mateusznowakdev/door-controller/firmware/app/core.py

import asyncio
import board
import keypad
import rtc as _rtc
import time
from busio import I2C
from digitalio import DigitalInOut, Direction, Pull
from microcontroller import watchdog
from pwmio import PWMOut
from watchdog import WatchDogMode

from adafruit_24lc32 import EEPROM_I2C
from adafruit_character_lcd.character_lcd import Character_LCD_Mono
from adafruit_ds3231 import DS3231

from app import const
from app.shared import _, get_checksum, get_time_offsets, log, verify_checksum
from app.types import HistoryT, SettingsT, TaskT

WDT_PIN = board.GP28

LCD_RS_PIN = board.GP9
LCD_EN_PIN = board.GP8
LCD_DB4_PIN = board.GP7
LCD_DB5_PIN = board.GP6
LCD_DB6_PIN = board.GP5
LCD_DB7_PIN = board.GP4
LCD_BL_PIN = board.GP3

KEY_LEFT_PIN = board.GP13
KEY_RIGHT_PIN = board.GP14
KEY_ENTER_PIN = board.GP15

I2C_SCL_PIN = board.GP11
I2C_SDA_PIN = board.GP10


class _WatchDog:
    TIMEOUT = 8.0

    def __init__(self) -> None:
        self.wdt_pin = DigitalInOut(WDT_PIN)
        self.wdt_pin.direction = Direction.INPUT
        self.wdt_pin.pull = Pull.DOWN
        self.enabled = False

    def feed(self) -> None:
        # watchdog will be enabled as soon as wdt_pin is detected to be HIGH,
        # and it cannot be disabled until restart

        if not self.enabled and self.wdt_pin.value is True:
            watchdog.timeout = self.TIMEOUT
            watchdog.mode = WatchDogMode.RESET
            self.enabled = True

            log("Watchdog initialized")

        if self.enabled:
            watchdog.feed()


class _Logger:
    FIRST_BYTE = 1024
    LAST_BYTE = 2048

    FRAME_SIZE = 8

    END_FRAME = [255, 0, 0, 0, 0, 0, 0]
    END_FRAME.append(get_checksum(END_FRAME))

    def __init__(self) -> None:
        self.address = self.FIRST_BYTE

        # copy EEPROM to RAM
        raw = eeprom[self.FIRST_BYTE : self.LAST_BYTE]

        for address in range(self.FIRST_BYTE, self.LAST_BYTE, self.FRAME_SIZE):
            first = address - self.FIRST_BYTE
            last = first + self.FRAME_SIZE

            if raw[first:last] == bytearray(self.END_FRAME):
                # found location for the next write
                self.address = address
                break

    def get(self, log_id: int) -> HistoryT:
        # self.address is the location of the end frame
        # so the #0 is self.address-8
        #        #1 is self.address-16, and so on
        address = self.address - (log_id + 1) * self.FRAME_SIZE

        # handle wraparound
        while address < self.FIRST_BYTE:
            address += self.LAST_BYTE - self.FIRST_BYTE

        raw = eeprom[address : address + self.FRAME_SIZE]
        if not verify_checksum(raw):
            return HistoryT(255, 0, 0, 0)

        return HistoryT(raw[0], raw[1], raw[2], raw[3])

    def log(self, message_id: int) -> None:
        log(_(message_id))

        now = time.localtime()

        raw = [message_id, now.tm_hour, now.tm_min, now.tm_sec, 0, 0, 0]
        raw.append(get_checksum(raw))

        # write log data
        first = self.address
        last = first + self.FRAME_SIZE
        eeprom[first:last] = bytearray(raw)
        self.address += self.FRAME_SIZE

        # handle wraparound
        if self.address >= self.LAST_BYTE:
            self.address = self.FIRST_BYTE

        # write end frame data
        # the same address will be used for next log write
        first = self.address
        last = first + self.FRAME_SIZE
        eeprom[first:last] = self.END_FRAME


class _Motor:
    # action ID describes the first EEPROM address for its settings
    ACT_OPEN = 512
    ACT_CLOSE = 512 + 8

    REASON_ONESHOT = 0
    REASON_AUTO = 1
    REASON_MEASURE = 2

    def __init__(self) -> None:
        self.lock = None

        self._ch1 = DigitalInOut(board.GP18)
        self._ch1.direction = Direction.OUTPUT
        self._ch1.value = False

        self._ch2 = DigitalInOut(board.GP19)
        self._ch2.direction = Direction.OUTPUT
        self._ch2.value = False

        self._ch3 = DigitalInOut(board.GP20)
        self._ch3.direction = Direction.OUTPUT
        self._ch3.value = False

        self._ch4 = DigitalInOut(board.GP21)
        self._ch4.direction = Direction.OUTPUT
        self._ch4.value = False

    def sleep(self, duration: float) -> None:
        loop_duration = wdt.TIMEOUT / 2

        while duration > 0:
            wdt.feed()
            time.sleep(loop_duration if duration > loop_duration else duration)
            duration -= loop_duration

        wdt.feed()

    async def asleep(self, duration: float) -> None:
        loop_duration = 0.5

        while duration > 0:
            wdt.feed()
            await asyncio.sleep(loop_duration if duration > loop_duration else duration)
            duration -= loop_duration

        wdt.feed()

    def open_start(self, reason_id: int) -> bool:
        if self.lock:
            return False

        logger.log(const.ACT_OPEN_START + reason_id)

        self.lock = object()
        self._ch1.value = False
        self._ch2.value = True

        return True

    def open_stop(self) -> None:
        self._ch1.value = False
        self._ch2.value = False
        self.lock = None

        logger.log(const.ACT_OPEN_STOP)

    def open(self, reason_id: int, duration: float) -> None:
        if not self.open_start(reason_id):
            return

        self.sleep(duration)
        self.open_stop()

    async def aopen(self, reason_id: int, duration: float) -> None:
        if not self.open_start(reason_id):
            return

        try:
            await self.asleep(duration)
        finally:
            self.open_stop()

    def close_start(self, reason_id: int) -> bool:
        if self.lock:
            return False

        logger.log(const.ACT_CLOSE_START + reason_id)

        self.lock = object()
        self._ch3.value = False
        self._ch4.value = True

        return True

    def close_stop(self) -> None:
        self._ch3.value = False
        self._ch4.value = False
        self.lock = None

        logger.log(const.ACT_CLOSE_STOP)

    def close(self, reason_id: int, duration: float) -> None:
        if not self.close_start(reason_id):
            return

        self.sleep(duration)
        self.close_stop()

    async def aclose(self, reason_id: int, duration: float) -> None:
        if not self.close_start(reason_id):
            return

        try:
            await self.asleep(duration)
        finally:
            self.close_stop()


class _Display:
    WIDTH = 16
    HEIGHT = 2

    BACKLIGHT_HIGH = 50
    BACKLIGHT_LOW = 15
    BACKLIGHT_OFF = 1

    CHAR_OPEN = 0, 0b11000, 0b10110, 0b10001, 0b10110, 0b11000, 0, 0
    CHAR_CLOSE = 0, 0b00011, 0b01101, 0b10001, 0b01101, 0b00011, 0, 0
    CHAR_SET_OPEN = 0, 0b11000, 0b10110, 0b00001, 0b11010, 0b11000, 0, 0
    CHAR_SET_CLOSE = 0, 0b00011, 0b01101, 0b10000, 0b01011, 0b00011, 0, 0
    CHAR_SET_SYSTEM = 0, 0b00100, 0b00010, 0b10010, 0b01110, 0b00001, 0, 0
    CHAR_TIME = 0, 0b01110, 0b10101, 0b10111, 0b10001, 0b01110, 0, 0
    CHAR_OK = 0, 0b00001, 0b00010, 0b00100, 0b10100, 0b01000, 0, 0
    CHAR_CANCEL = 0, 0b10001, 0b01010, 0b00100, 0b01010, 0b10001, 0, 0
    CHAR_CURSOR_L = 0b00101, 0b00000, 0b00100, 0, 0, 0b00100, 0b00000, 0b00101
    CHAR_CURSOR_R = 0b10100, 0b00000, 0b00100, 0, 0, 0b00100, 0b00000, 0b10100
    CHAR_CURSOR_ALT_L = 0b00111, 0b00100, 0b00100, 0, 0, 0b00100, 0b00100, 0b00111
    CHAR_CURSOR_ALT_R = 0b11100, 0b00100, 0b00100, 0, 0, 0b00100, 0b00100, 0b11100

    def __init__(self) -> None:
        self._display = Character_LCD_Mono(
            rs=DigitalInOut(LCD_RS_PIN),
            en=DigitalInOut(LCD_EN_PIN),
            db4=DigitalInOut(LCD_DB4_PIN),
            db5=DigitalInOut(LCD_DB5_PIN),
            db6=DigitalInOut(LCD_DB6_PIN),
            db7=DigitalInOut(LCD_DB7_PIN),
            columns=self.WIDTH,
            lines=self.HEIGHT,
        )
        self._display.create_char(0, self.CHAR_OPEN)
        self._display.create_char(1, self.CHAR_CLOSE)
        self.set_default_icons()
        self._display.create_char(4, self.CHAR_SET_SYSTEM)
        self._display.create_char(5, self.CHAR_TIME)
        self.set_default_cursor()

        self._cur_buffer = bytearray(b" " * self.WIDTH * self.HEIGHT)
        self._old_buffer = self._cur_buffer[:]
        self.clear()

        self._backlight = PWMOut(LCD_BL_PIN)
        self.set_backlight(self.BACKLIGHT_OFF)

    def clear(self) -> None:
        self._cur_buffer[:] = b" " * len(self._cur_buffer)

    def write(self, pos: tuple[int, int], data: bytes) -> None:
        col, row = pos
        byte_id = row * self.WIDTH + col

        self._cur_buffer[byte_id : byte_id + len(data)] = data

    def flush(self) -> None:
        if self._cur_buffer == self._old_buffer:
            return

        lines = []

        for row in range(0, self.HEIGHT):
            first_byte_id = row * self.WIDTH
            last_byte_id = (row + 1) * self.WIDTH

            line = "".join(chr(b) for b in self._cur_buffer[first_byte_id:last_byte_id])
            lines.append(line)

        self._display.message = "\n".join(lines)
        self._old_buffer = self._cur_buffer[:]

    def set_default_icons(self) -> None:
        self._display.create_char(2, self.CHAR_SET_OPEN)
        self._display.create_char(3, self.CHAR_SET_CLOSE)

    def set_alternate_icons(self) -> None:
        self._display.create_char(2, self.CHAR_OK)
        self._display.create_char(3, self.CHAR_CANCEL)

    def set_default_cursor(self) -> None:
        self._display.create_char(6, self.CHAR_CURSOR_L)
        self._display.create_char(7, self.CHAR_CURSOR_R)

    def set_alternate_cursor(self) -> None:
        self._display.create_char(6, self.CHAR_CURSOR_ALT_L)
        self._display.create_char(7, self.CHAR_CURSOR_ALT_R)

    def set_backlight(self, value: int) -> None:
        self._backlight.duty_cycle = value * 65535 // 100


class _Keys:
    LEFT = 0
    RIGHT = 1
    ENTER = 2

    HOLD_KEYS = [LEFT, RIGHT]
    HOLD_THRESHOLD = 1.0

    def __init__(self) -> None:
        self._keys = keypad.Keys(
            pins=(KEY_LEFT_PIN, KEY_RIGHT_PIN, KEY_ENTER_PIN),
            value_when_pressed=False,
            max_events=1,
        )

        self._key_number = None
        self._key_timestamp = 0.0
        self._press_read = False

    def get(self) -> tuple[int | None, float]:
        event = None
        while last_event := self._keys.events.get():
            event = last_event

        if event:
            if event.pressed:
                self._key_number = event.key_number
                self._key_timestamp = time.monotonic()
                self._press_read = False
            else:
                self._key_number = None
                self._key_timestamp = 0.0

        # no key is pressed
        if self._key_number is None:
            return None, 0.0

        # supported key is held
        diff = time.monotonic() - self._key_timestamp
        if self._key_number in self.HOLD_KEYS and diff > self.HOLD_THRESHOLD:
            return self._key_number, diff

        # key is pressed but it was acknowledged
        if self._press_read:
            return None, 0.0

        # key is pressed
        self._press_read = True
        return self._key_number, 0.0


class _Settings:
    DEFAULTS = SettingsT(0, 0, 0, 0, 0, 1)

    VERSION = 1
    HEADER = bytearray((80, 73, 67, VERSION))

    def __init__(self) -> None:
        # handle first boot
        if eeprom[0 : len(self.HEADER)] != self.HEADER:
            eeprom[0 : len(self.HEADER)] = self.HEADER
            self.reset()

    def load(self, action_id: int) -> SettingsT:
        raw = eeprom[action_id : action_id + 8]

        if not verify_checksum(raw):
            logger.log(const.SETTINGS_ERROR)
            return self.DEFAULTS

        return SettingsT(raw[0], raw[1], raw[2], raw[3], raw[4] + raw[5] * 256, raw[6])

    def save(self, action_id: int, obj: SettingsT) -> None:
        self.save_nolog(action_id, obj)
        logger.log(const.SETTINGS_SAVE)

    def save_nolog(self, action_id: int, obj: SettingsT) -> None:
        raw = [obj[0], obj[1], obj[2], obj[3], obj[4] % 256, obj[4] // 256, obj[5]]
        raw.append(get_checksum(raw))
        eeprom[action_id : action_id + 8] = bytearray(raw)

    def reset(self) -> None:
        self.save_nolog(motor.ACT_OPEN, self.DEFAULTS)
        self.save_nolog(motor.ACT_CLOSE, self.DEFAULTS)
        logger.log(const.SETTINGS_RESET)


class _Scheduler:
    def __init__(self) -> None:
        self.tasks = self.get_tasks()

    def restart(self) -> None:
        self.tasks = self.get_tasks()

    def get_tasks(self) -> list[TaskT]:
        if rtc.lost_power:
            logger.log(const.SCHEDULER_ERROR)
            return []

        opening_tasks = self.get_tasks_for_action(motor.ACT_OPEN)
        closing_tasks = self.get_tasks_for_action(motor.ACT_CLOSE)

        logger.log(const.SCHEDULER_INIT)
        return opening_tasks + closing_tasks

    def get_tasks_for_action(self, action_id: int) -> list[TaskT]:
        tasks = []

        now = time.localtime()
        now_ts = time.mktime(now)

        midnight_ts = time.mktime(
            (now.tm_year, now.tm_mon, now.tm_mday, 0, 0, 0, 0, 0, -1)
        )

        motor_settings = settings.load(action_id)
        offsets = get_time_offsets(motor_settings)

        reason = motor.REASON_AUTO

        for offset in offsets:
            # add extra 5s delay before any task can be run
            ts = midnight_ts + offset
            while ts < now_ts + 5 * const.SECOND:
                ts += const.DAY

            if action_id == motor.ACT_OPEN:
                fn = lambda: motor.open(reason, motor_settings.duration_single)
            elif action_id == motor.ACT_CLOSE:
                fn = lambda: motor.close(reason, motor_settings.duration_single)
            else:
                raise ValueError("Unknown action ID")

            task = TaskT(action_id, ts, fn)
            tasks.append(task)

        return tasks

    async def loop(self) -> None:
        wdt.feed()
        await asyncio.sleep(wdt.TIMEOUT / 2)

        now = time.time()

        for idx, task in enumerate(self.tasks):
            if now < task.timestamp:
                continue

            task.function()

            ts = task.timestamp + const.DAY
            self.tasks[idx] = TaskT(task.action_id, ts, task.function)

            # skip processing other operations for now
            return


wdt = _WatchDog()
wdt.feed()

i2c = I2C(scl=I2C_SCL_PIN, sda=I2C_SDA_PIN)
log("I2C initialized")

rtc = DS3231(i2c)
_rtc.set_time_source(rtc)
log("RTC initialized")

eeprom = EEPROM_I2C(i2c, 0x57)
log("EEPROM initialized")

motor = _Motor()
log("Motor initialized")

display = _Display()
log("Display initialized")

keys = _Keys()
log("Keys initialized")

logger = _Logger()
logger.log(const.BOARD_INIT)

settings = _Settings()
scheduler = _Scheduler()


async def loop() -> None:
    while True:
        await scheduler.loop()
