mateusznowakdev/door-controller/firmware/app/shared.py

import math
import time

from app import const
from app.types import SettingsT

BASE_CHECKSUM = 42


def _(text_id: int) -> str:
    return const.TRANSLATIONS.get(const.LANG, {}).get(text_id, f"{text_id}?")


def chunk(items: list, size: int) -> list[tuple]:
    chunk_count = math.ceil(len(items) / size)
    return [items[x * size : (x + 1) * size] for x in range(chunk_count)]


def clamp(value: int, low: int, hi: int) -> int:
    return max(min(value, hi), low)


def format_time(hour: int, minute: int, second: int | None = None) -> bytes:
    if second is None:
        return f"{hour:02}:{minute:02}".encode()

    return f"{hour:02}:{minute:02}:{second:02}".encode()


def get_checksum(data: list[int]) -> int:
    result = BASE_CHECKSUM

    for value in data:
        result ^= value

    return result


def get_time_offsets(settings: SettingsT) -> list[int]:
    first_sec = settings.first_hr * const.HOUR + settings.first_min * const.MINUTE
    last_sec = settings.last_hr * const.HOUR + settings.last_min * const.MINUTE

    if settings.duration == 0:
        return []
    if settings.divided_by < 2:
        return [first_sec]

    # handle night schedule
    if first_sec > last_sec:
        last_sec += const.DAY

    total_distance = last_sec - first_sec
    distance = total_distance / (settings.divided_by - 1)

    offsets = []
    for idx in range(settings.divided_by):
        offsets.append(round(first_sec + idx * distance) % const.DAY)

    return offsets


def log(message: str) -> None:
    print(f"[{time.monotonic():10.2f}] {message}")


def verify_checksum(data: list[int]) -> bool:
    return get_checksum(data[:-1]) == data[-1]
